grodansparadis/can4vscp_accra/docs/images/accra1.png

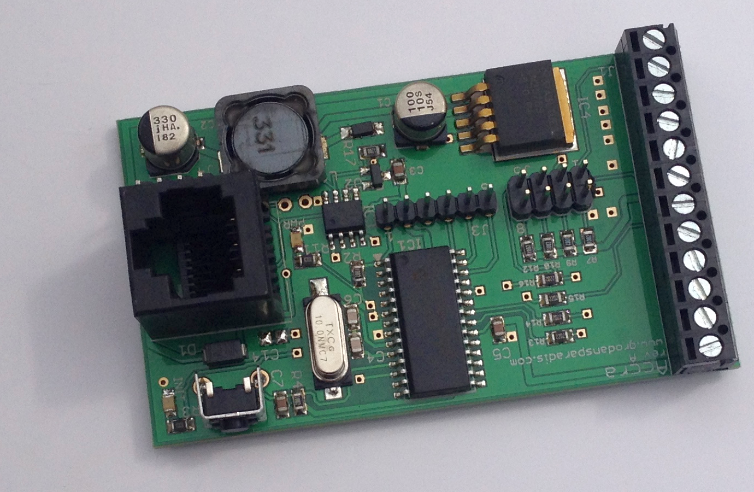
docs/images/accra1.png
