grodansparadis/can4vscp_accra/docs/images/accra2.png

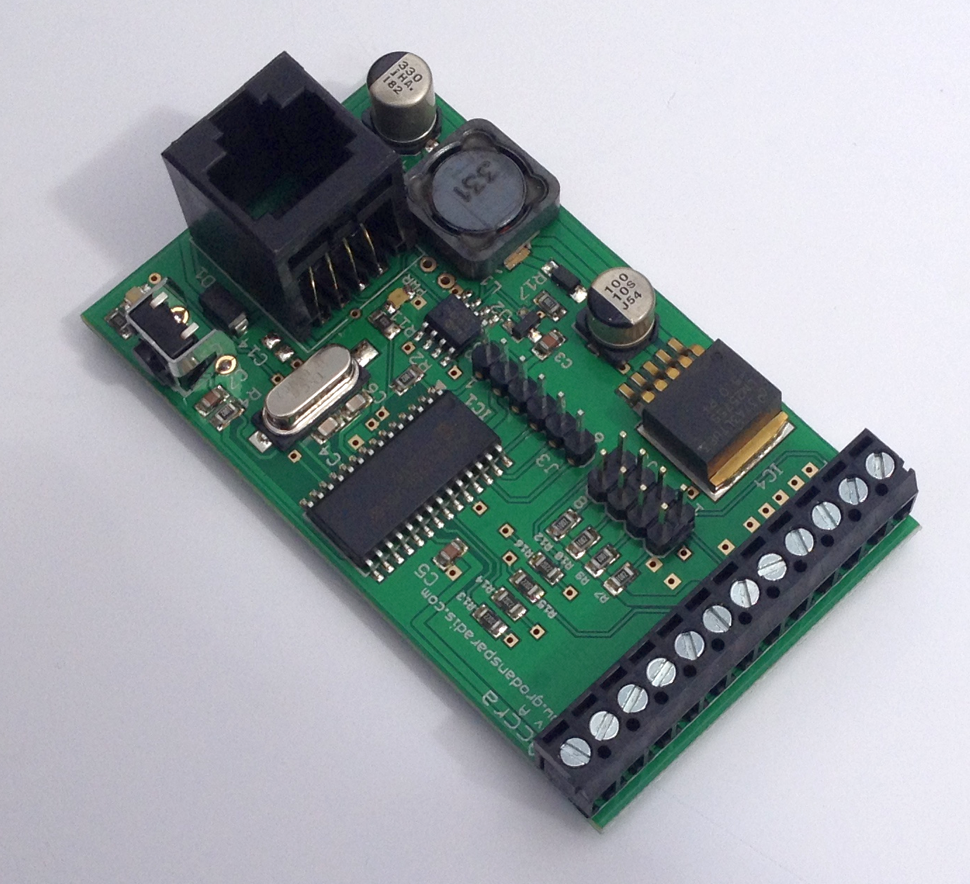
docs/images/accra2.png
