grodansparadis/can4vscp_accra/docs/images/accra4.png

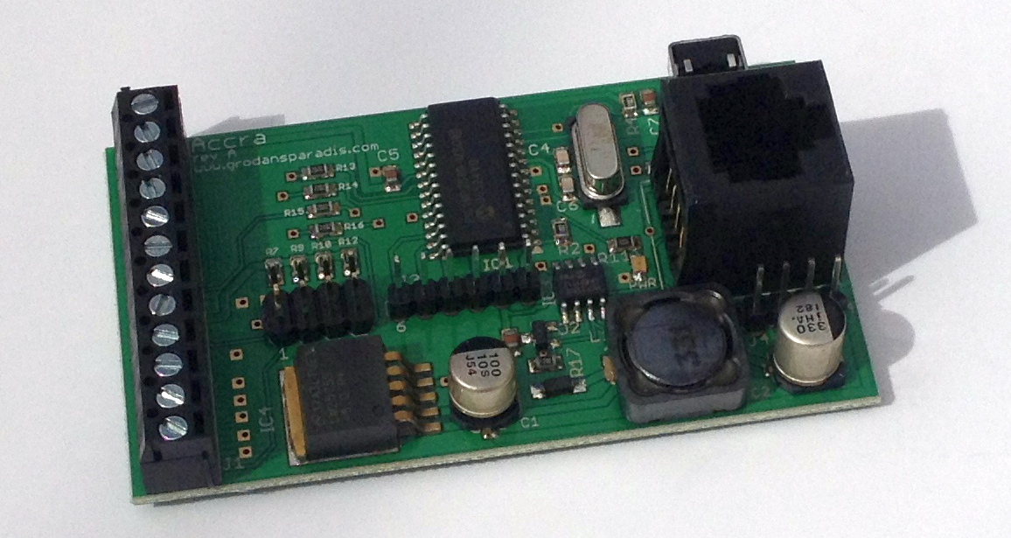
docs/images/accra4.png
