grodansparadis/can4vscp_accra/docs/images/accra5.png

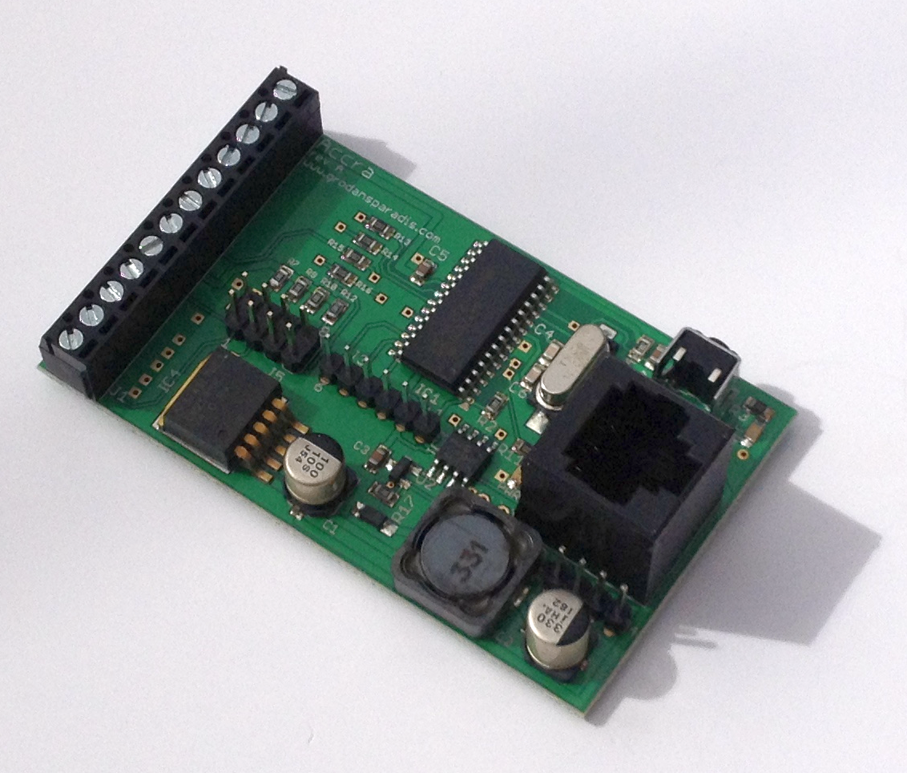
docs/images/accra5.png
