grodansparadis/can4vscp_accra/docs/images/accra8.png

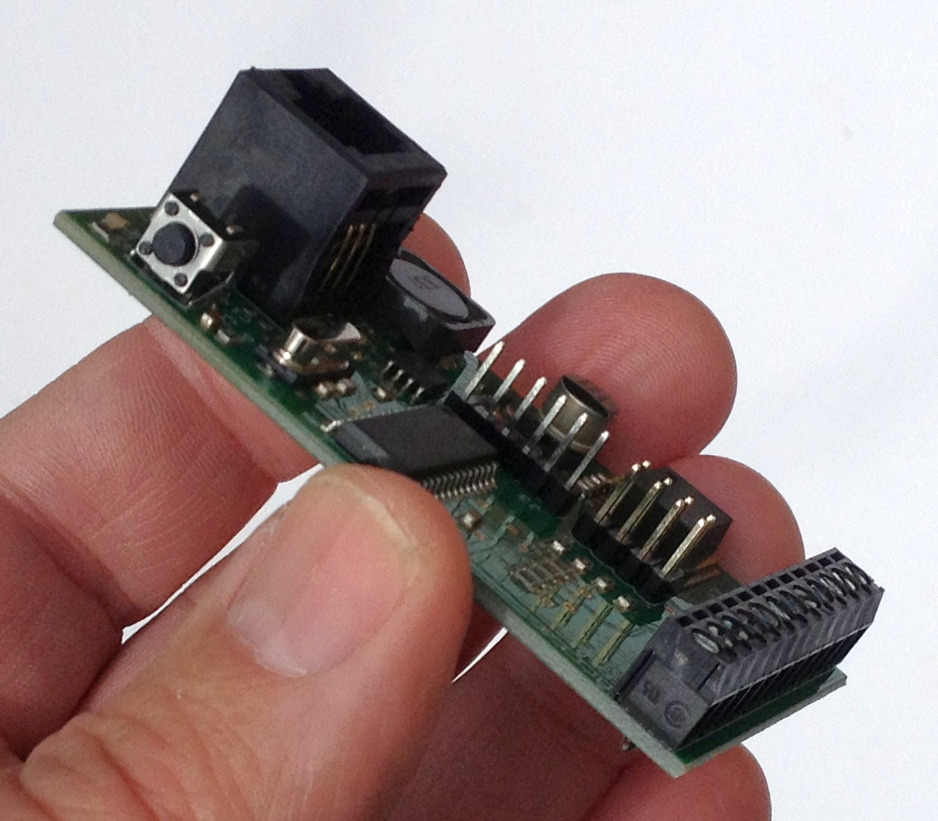
docs/images/accra8.png
