grodansparadis/can4vscp_accra/docs/images/accra9.png

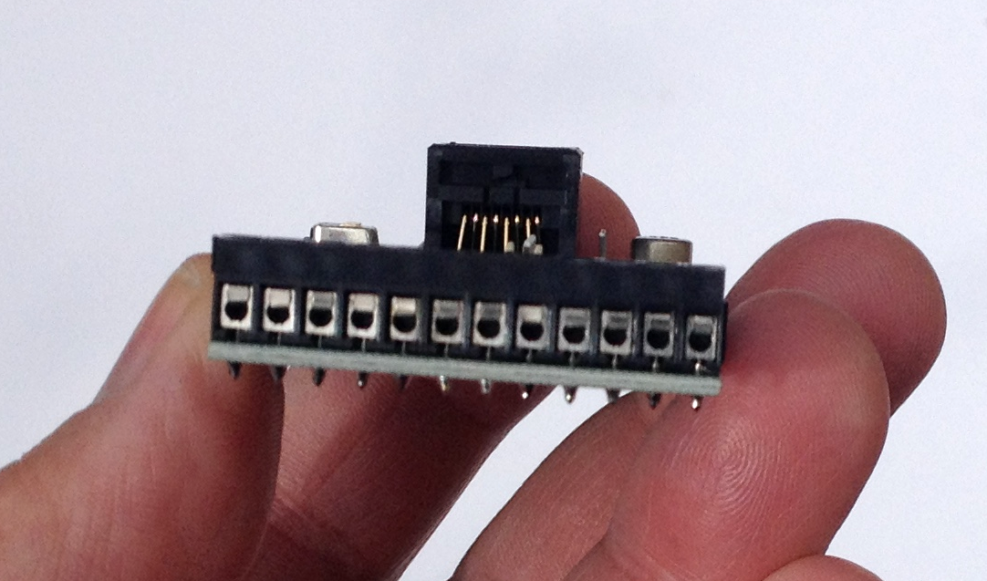
docs/images/accra9.png
