grodansparadis/can4vscp_accra/docs/images/accra10.png

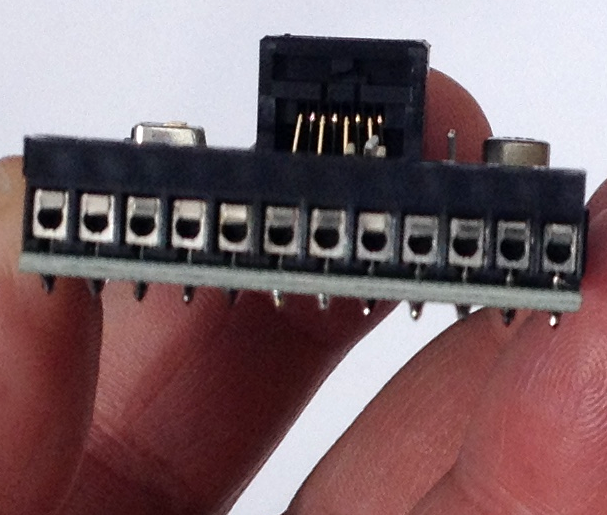
docs/images/accra10.png
