grodansparadis/can4vscp_accra/docs/images/accra11.png

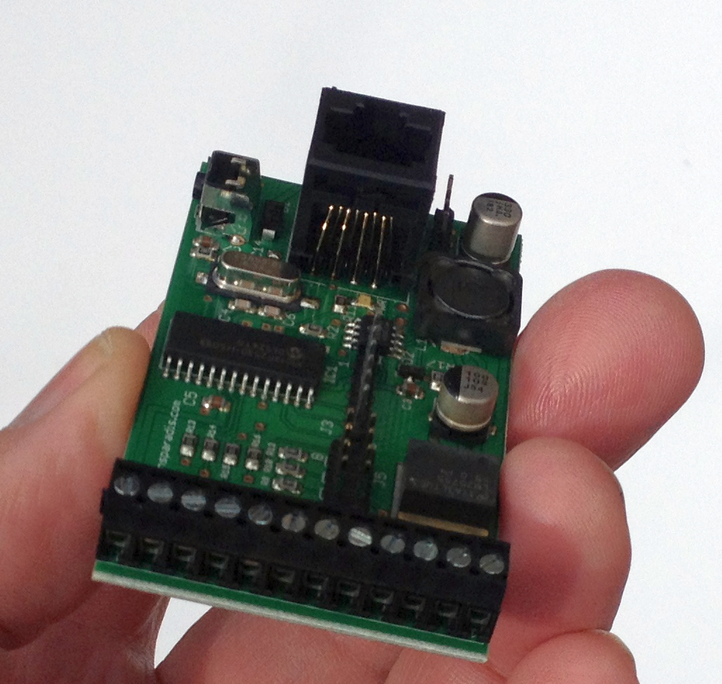
docs/images/accra11.png
