grodansparadis/can4vscp_accra/docs/images/accra12.png

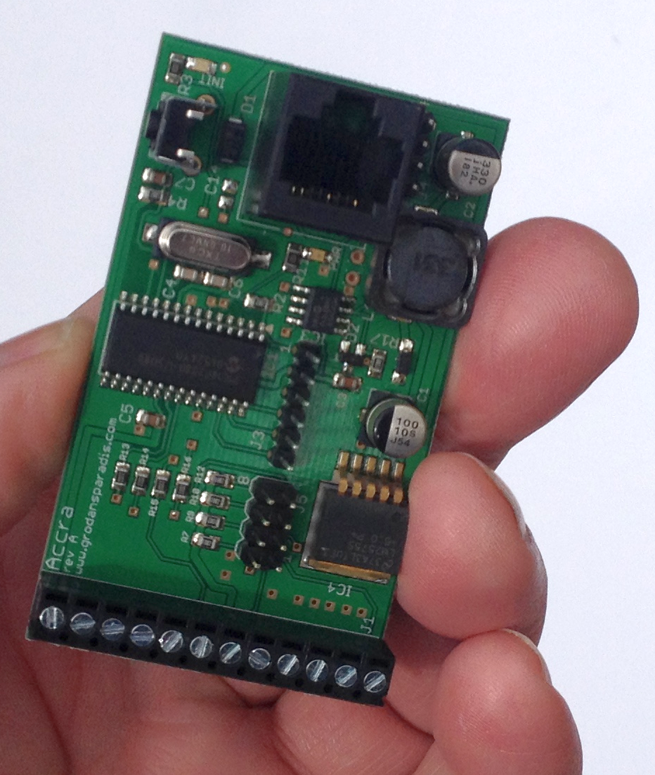
docs/images/accra12.png
