grodansparadis/can4vscp_accra/docs/images/accra13.png

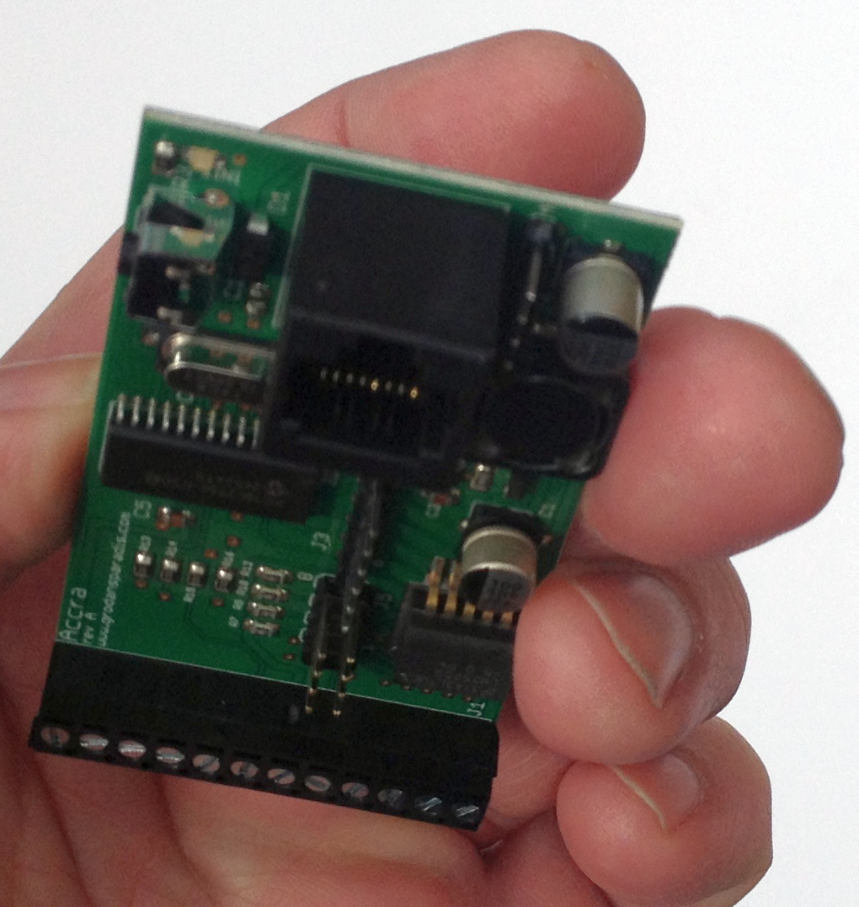
docs/images/accra13.png
