grodansparadis/can4vscp_accra/docs/misc/1425977499.jpg

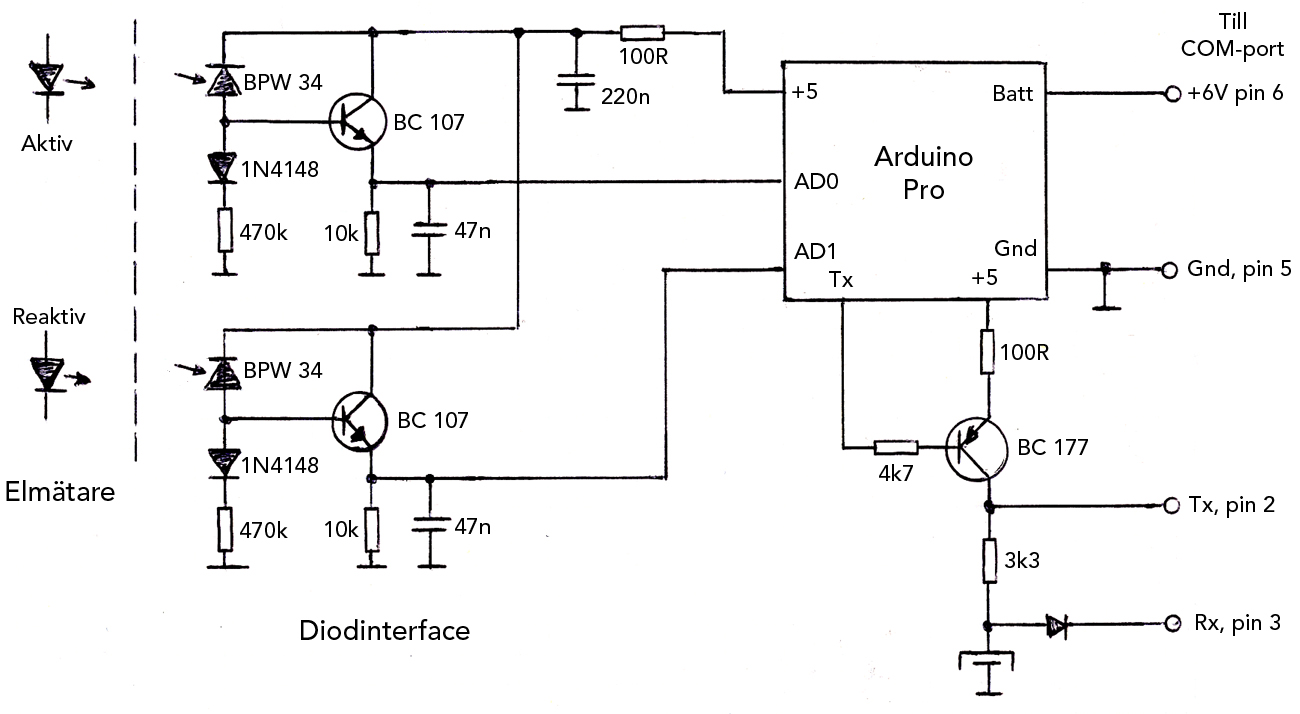
docs/misc/1425977499.jpg
