grodansparadis/can4vscp_accra/docs/misc/elmschema.jpg

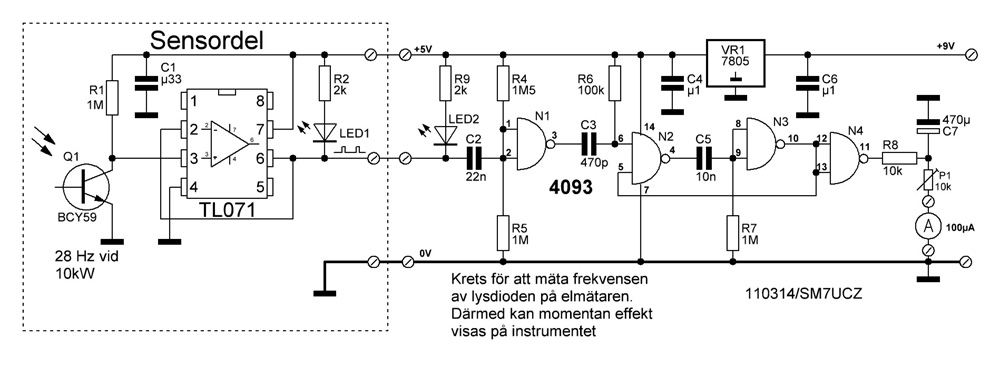
docs/misc/elmschema.jpg
