grodansparadis/can4vscp_accra/docs/misc/h21018.jpg

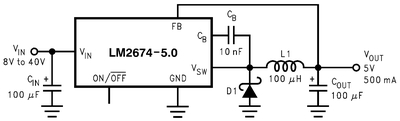
docs/misc/h21018.jpg
