grodansparadis/can4vscp_accra/docs/misc/Screenshot_from_2016-03-12_185128.png

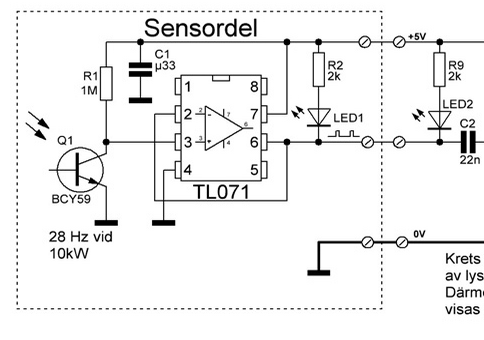
docs/misc/Screenshot_from_2016-03-12_185128.png
